hyperion11/Toyota-Prado-OBD1-Computer/source/TOBD1_STM32/atf_temp_sensor_1.png

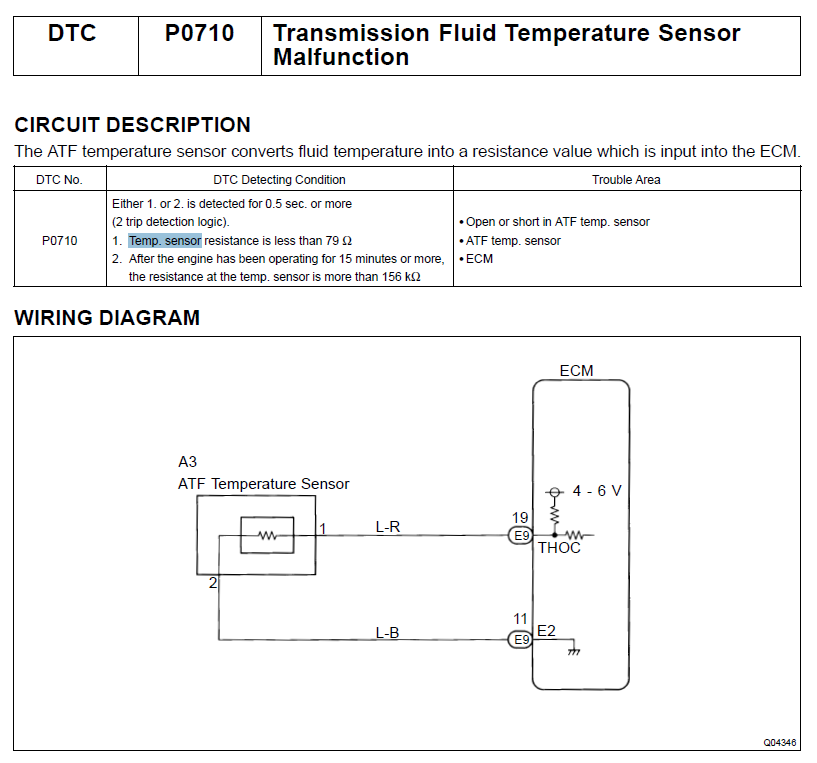
source/TOBD1_STM32/atf_temp_sensor_1.png
