hyperion11/Toyota-Prado-OBD1-Computer/BK Model/крепеж_дисплея_v2.3.STEP

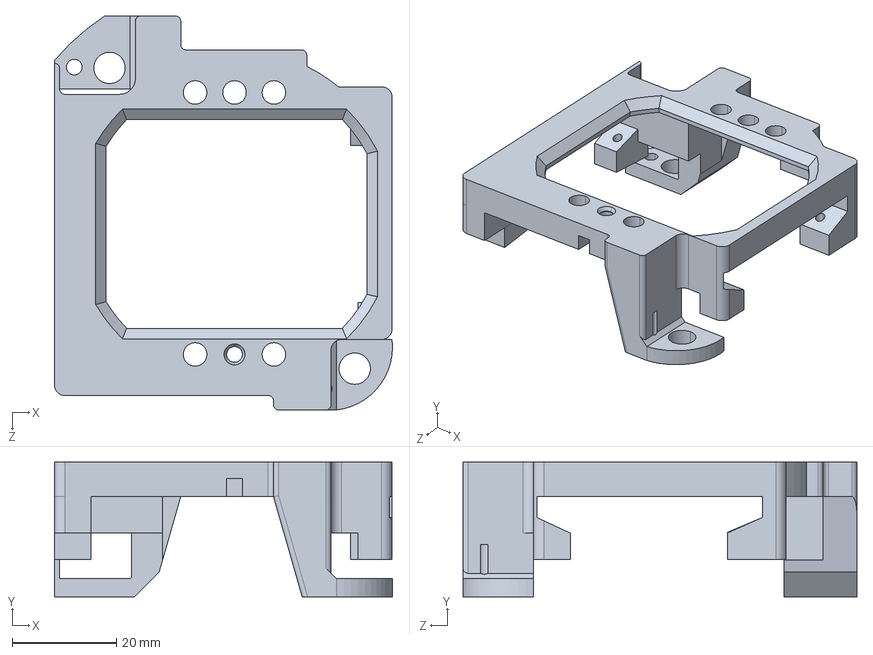
[picture p21: CAD file, 2021-05-25]
BK Model/крепеж_дисплея_v2.3.STEP
64.8 x 25.8 x 75.5 mm
