hyperion11/Toyota-Prado-OBD1-Computer/BK Model/крепеж_дисплея_1_v4.SLDPRT

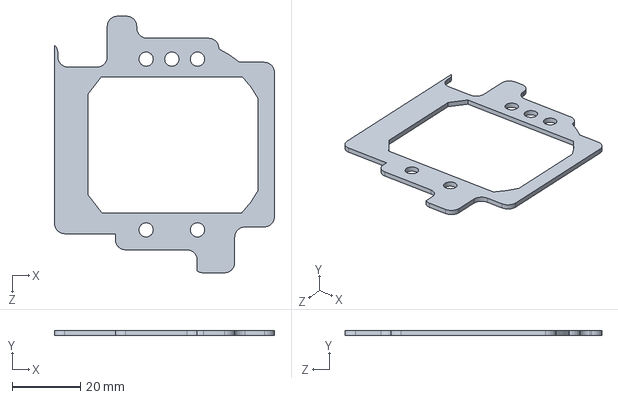
[picture p22: CAD file, 2021-05-25]
BK Model/крепеж_дисплея_1_v4.SLDPRT
64.7 x 1.50 x 75.5 mm
