hyperion11/Toyota-Prado-OBD1-Computer/BK Model/front_shield.SLDPRT

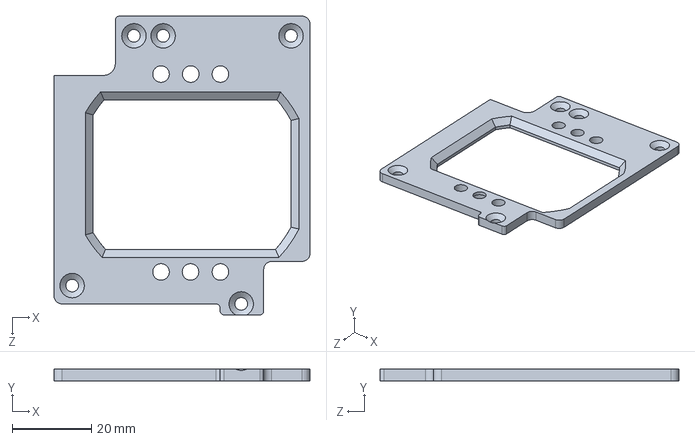
[picture p23: CAD file, 2021-05-25]
BK Model/front_shield.SLDPRT
64.7 x 3.00 x 75.5 mm
