hyperion11/Toyota-Prado-OBD1-Computer/BK Model/pcb_shield.SLDPRT

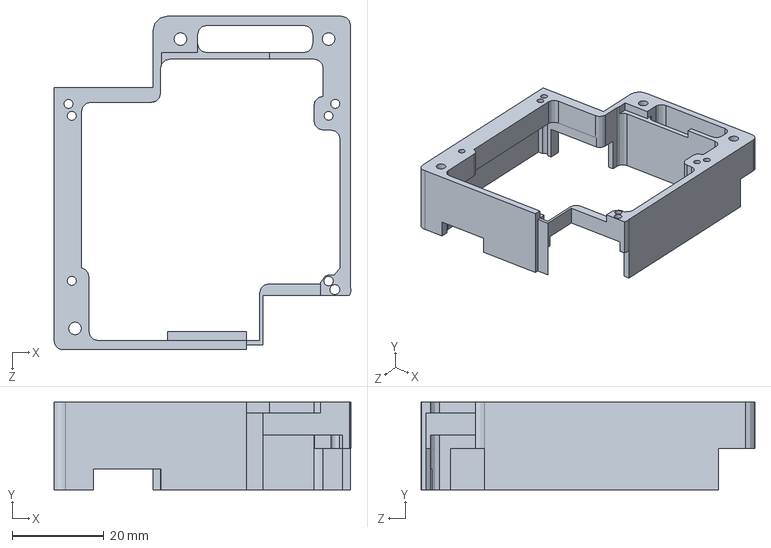
[picture p24: CAD file, 2021-05-25]
BK Model/pcb_shield.SLDPRT
64.8 x 19.1 x 72.8 mm
