hyperion11/Toyota-Prado-OBD1-Computer/source/TOBD1_STM32/src/CPMonoP9pt7b.h

const uint8_t CPMono_v07_Plain9pt7bBitmaps[] PROGMEM = {
  0xFF, 0xFF, 0xCF, 0xDE, 0xF7, 0xB0, 0x36, 0x1B, 0x3F, 0xFF, 0xF3, 0x67,
  0xBF, 0xFE, 0x6C, 0x36, 0x00, 0x0C, 0x3F, 0x9F, 0xF8, 0x3C, 0x06, 0x01,
  0xFC, 0x7F, 0x01, 0x80, 0xF0, 0x6F, 0xF7, 0xF0, 0x60, 0xF0, 0x90, 0x90,
  0x90, 0xF1, 0x07, 0x1C, 0xE0, 0x9E, 0x13, 0x13, 0x13, 0x13, 0x1E, 0x7F,
  0x0F, 0xF3, 0x06, 0x60, 0x0C, 0x18, 0xF7, 0xDE, 0x7E, 0x0C, 0xC1, 0x98,
  0x31, 0xFE, 0x3F, 0x80, 0xFF, 0x7B, 0xF1, 0x8C, 0x63, 0x18, 0xC6, 0x31,
  0x8C, 0x63, 0x0F, 0x78, 0xF7, 0xC6, 0x31, 0x8C, 0x63, 0x18, 0xC6, 0x31,
  0x8C, 0x7F, 0xF0, 0x0C, 0x06, 0x1B, 0x6F, 0xE1, 0xC3, 0xF9, 0xB6, 0x18,
  0x0C, 0x00, 0x18, 0x18, 0x18, 0x18, 0xFF, 0xFF, 0x18, 0x18, 0x18, 0x6C,
  0xE0, 0xFF, 0xF0, 0xF0, 0x06, 0x0C, 0x18, 0x60, 0xC1, 0x86, 0x0C, 0x18,
  0x60, 0xC1, 0x86, 0x0C, 0x18, 0x60, 0x7F, 0x7F, 0xF0, 0x78, 0x3C, 0x1E,
  0x0F, 0x07, 0x83, 0xC1, 0xE0, 0xFF, 0xEF, 0xE0, 0xF8, 0x7C, 0x06, 0x03,
  0x01, 0x80, 0xC0, 0x60, 0x30, 0x18, 0x0C, 0x3F, 0xFF, 0xF0, 0x7F, 0x3F,
  0xEC, 0x19, 0x06, 0x01, 0x80, 0xC0, 0x60, 0x70, 0x38, 0x1C, 0x0F, 0xFF,
  0xFF, 0x7F, 0x7F, 0xF0, 0x60, 0x30, 0x18, 0xFC, 0x7E, 0x03, 0x01, 0xE0,
  0xFF, 0xEF, 0xE0, 0x07, 0x03, 0xC0, 0xF0, 0x6C, 0x33, 0x1C, 0xCE, 0x33,
  0xFF, 0xFF, 0xC0, 0xC0, 0x30, 0x0C, 0xFF, 0xFF, 0xC0, 0xC0, 0xFE, 0xFF,
  0xC3, 0x03, 0x03, 0xC3, 0xFF, 0xFE, 0x7F, 0x3F, 0xF0, 0x78, 0x2C, 0x07,
  0xFB, 0xFF, 0x83, 0xC1, 0xE0, 0xDF, 0xEF, 0xE0, 0xFF, 0xFF, 0xC0, 0x60,
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
  {   395,   8,  12,  11,    2,  -11 },   // 0x46 'F'
  {   407,   9,  12,  11,    1,  -11 },   // 0x47 'G'
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

const GFXfont CPMono_v07_Plain9pt7b PROGMEM = {
  (uint8_t  *)CPMono_v07_Plain9pt7bBitmaps,
  (GFXglyph *)CPMono_v07_Plain9pt7bGlyphs,
  0x20, 0x7E, 25 };

// Approx. 1758 bytes
