hyperion11/Toyota-Prado-OBD1-Computer/source/TOBD1_STM32/src/CPMono_L13pt7b.h

const uint8_t CPMono_v07_Plain13pt7bBitmaps[] PROGMEM = {
  0xFF, 0xFF, 0xFF, 0xFF, 0xFE, 0x3F, 0xE0, 0xCF, 0x9F, 0x3E, 0x7C, 0xE0,
  0x19, 0xC0, 0xCE, 0x06, 0x71, 0xFF, 0xFF, 0xFF, 0x8C, 0x60, 0x63, 0x03,
  0x18, 0xFF, 0xFF, 0xFF, 0xC6, 0x70, 0x33, 0x81, 0x9C, 0x00, 0x06, 0x00,
  0x60, 0x3F, 0xE7, 0xFF, 0xF0, 0xFE, 0x03, 0xE0, 0x0E, 0x00, 0xE0, 0x0F,
  0xFE, 0x7F, 0xF0, 0x07, 0x00, 0x30, 0x03, 0x60, 0x3E, 0x03, 0xF0, 0xF7,
  0xFF, 0x3F, 0xE0, 0x60, 0x06, 0x00, 0x78, 0x1F, 0x82, 0x30, 0x46, 0x08,
  0xC1, 0x18, 0x3F, 0x07, 0xC3, 0x01, 0xE0, 0xF0, 0x70, 0x38, 0x0C, 0x38,
  0x0F, 0xC3, 0x18, 0x63, 0x0C, 0x61, 0x8C, 0x3F, 0x83, 0xE0, 0x7F, 0xE1,
  0xFF, 0xE3, 0xC3, 0xC6, 0x01, 0x8C, 0x00, 0x18, 0x06, 0x38, 0x0C, 0x3E,
  0xFF, 0x7D, 0xFF, 0xC0, 0x63, 0x00, 0xC6, 0x01, 0x8C, 0x03, 0x18, 0x06,
  0x3C, 0x3C, 0x7F, 0xF8, 0x7F, 0xE0, 0xFF, 0xC0, 0x7F, 0xFE, 0x38, 0xE3,
  0x8E, 0x38, 0xE3, 0x8E, 0x38, 0xE3, 0x8E, 0x38, 0xE3, 0x8E, 0x38, 0xE3,
  0xC7, 0xCF, 0xFB, 0xF1, 0xC3, 0x0C, 0x30, 0xC3, 0x0C, 0x30, 0xC3, 0x0C,
  0x30, 0xC3, 0x0C, 0x30, 0xC3, 0x0C, 0xFF, 0xFE, 0x06, 0x00, 0x60, 0x06,
  0x06, 0x67, 0x7E, 0xF1, 0xFC, 0x0F, 0x01, 0xFC, 0x7E, 0xF6, 0x67, 0x06,
  0x00, 0x60, 0x02, 0x00, 0x07, 0x00, 0x70, 0x07, 0x00, 0x70, 0x07, 0x0F,
  0xFF, 0xFF, 0xF0, 0x70, 0x07, 0x00, 0x70, 0x07, 0x00, 0x70, 0x77, 0x73,
  0x36, 0xFF, 0xFF, 0xFF, 0x80, 0x00, 0xC0, 0x70, 0x18, 0x0E, 0x03, 0x80,
  0xC0, 0x70, 0x1C, 0x06, 0x03, 0x80, 0xE0, 0x30, 0x1C, 0x06, 0x01, 0x80,
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
  {   765,  12,  17,  17,    3,  -16 },   // 0x46 'F'
  {   791,  13,  17,  17,    2,  -16 },   // 0x47 'G'
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

const GFXfont CPMono_v07_Plain13pt7b PROGMEM = {
  (uint8_t  *)CPMono_v07_Plain13pt7bBitmaps,
  (GFXglyph *)CPMono_v07_Plain13pt7bGlyphs,
  0x20, 0x7E, 36 };

// Approx. 2808 bytes
