hyperion11/Toyota-Prado-OBD1-Computer/source/TOBD1_STM32/src/DSEG7ModernMini-Bold13pt7b.h

const uint8_t DSEG7ModernMini_Bold13pt7bBitmaps[] PROGMEM = {
  0xFF, 0x06, 0x0C, 0x18, 0x30, 0x60, 0xC1, 0x83, 0x06, 0x0C, 0x18, 0x30,
  0x60, 0xC1, 0xFE, 0xFF, 0x06, 0x0C, 0x18, 0x30, 0x60, 0xC1, 0x83, 0x06,
  0x0C, 0x18, 0x30, 0x60, 0xC1, 0xFE, 0xFF, 0x06, 0x0C, 0x18, 0x30, 0x60,
  0xC1, 0x83, 0x06, 0x0C, 0x18, 0x30, 0x60, 0xC1, 0xFE, 0xFF, 0x06, 0x0C,
  0x18, 0x30, 0x60, 0xC1, 0x83, 0x06, 0x0C, 0x18, 0x30, 0x60, 0xC1, 0xFE,
  0xFF, 0x06, 0x0C, 0x18, 0x30, 0x60, 0xC1, 0x83, 0x06, 0x0C, 0x18, 0x30,
  0x60, 0xC1, 0xFE, 0xFF, 0x06, 0x0C, 0x18, 0x30, 0x60, 0xC1, 0x83, 0x06,
  0x0C, 0x18, 0x30, 0x60, 0xC1, 0xFE, 0xFF, 0x06, 0x0C, 0x18, 0x30, 0x60,
  0xC1, 0x83, 0x06, 0x0C, 0x18, 0x30, 0x60, 0xC1, 0xFE, 0xFF, 0x06, 0x0C,
  0x18, 0x30, 0x60, 0xC1, 0x83, 0x06, 0x0C, 0x18, 0x30, 0x60, 0xC1, 0xFE,
  0xFF, 0x06, 0x0C, 0x18, 0x30, 0x60, 0xC1, 0x83, 0x06, 0x0C, 0x18, 0x30,
  0x60, 0xC1, 0xFE, 0xFF, 0x06, 0x0C, 0x18, 0x30, 0x60, 0xC1, 0x83, 0x06,
  0x0C, 0x18, 0x30, 0x60, 0xC1, 0xFE, 0xFF, 0x06, 0x0C, 0x18, 0x30, 0x60,
  0xC1, 0x83, 0x06, 0x0C, 0x18, 0x30, 0x60, 0xC1, 0xFE, 0x7F, 0xFF, 0xBF,
  0x80, 0x6F, 0x60, 0xFF, 0x06, 0x0C, 0x18, 0x30, 0x60, 0xC1, 0x83, 0x06,
  0x0C, 0x18, 0x30, 0x60, 0xC1, 0xFE, 0x3F, 0xFC, 0x8F, 0xFC, 0xE3, 0xF9,
  0xF0, 0x03, 0xF0, 0x03, 0xF0, 0x07, 0xF0, 0x07, 0xF0, 0x07, 0xF0, 0x07,
  0xF0, 0x07, 0xF0, 0x01, 0xE0, 0x00, 0x60, 0x03, 0x00, 0x07, 0x80, 0x07,
  0xE0, 0x07, 0xF0, 0x07, 0xF0, 0x07, 0xF0, 0x07, 0xE0, 0x07, 0xE0, 0x07,
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
  {   995,  16,  25,  20,    2,  -24 },   // 0x47 'G'
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

const GFXfont DSEG7ModernMini_Bold13pt7b PROGMEM = {
  (uint8_t  *)DSEG7ModernMini_Bold13pt7bBitmaps,
  (GFXglyph *)DSEG7ModernMini_Bold13pt7bGlyphs,
  0x20, 0x7E, 27 };

// Approx. 3722 bytes
