hyperion11/Toyota-Prado-OBD1-Computer/source/TOBD1_STM32/src/CPMono_L6pt7b.h

const uint8_t CPMono_v07_Light6pt7bBitmaps[] PROGMEM = {
  0xFD, 0xB4, 0x53, 0xF5, 0x3F, 0x51, 0x40, 0x23, 0xE8, 0x60, 0xF8, 0x10,
  0x61, 0xF8, 0x80, 0xE2, 0x8A, 0x39, 0x19, 0x89, 0x89, 0x24, 0x60, 0x7C,
  0x84, 0x84, 0x6F, 0x84, 0x84, 0x84, 0x7C, 0xC0, 0x72, 0x49, 0x24, 0x92,
  0x30, 0xE4, 0x92, 0x49, 0x24, 0xF0, 0x22, 0x87, 0x9E, 0xA0, 0x80, 0x20,
  0x82, 0x3F, 0x20, 0x80, 0xE0, 0xF0, 0x80, 0x08, 0x44, 0x23, 0x10, 0x88,
  0x42, 0x00, 0xFA, 0x18, 0x61, 0x86, 0x18, 0x7E, 0x70, 0x41, 0x04, 0x10,
  0x41, 0x3F, 0xFA, 0x10, 0x42, 0x10, 0x84, 0x3F, 0xFA, 0x10, 0x4E, 0x04,
  0x18, 0x7E, 0x0C, 0x0C, 0x14, 0x24, 0x44, 0xFF, 0x04, 0x04, 0xFE, 0x08,
  0x3E, 0x84, 0x18, 0x7E, 0xFA, 0x18, 0x3E, 0x86, 0x18, 0x7E, 0xFC, 0x20,
  0x84, 0x10, 0x82, 0x18, 0xFA, 0x18, 0x7E, 0x86, 0x18, 0x7E, 0xFA, 0x18,
  0x61, 0xFC, 0x18, 0x7E, 0x84, 0x87, 0x09, 0xB0, 0x60, 0x80, 0xF8, 0x3E,
  0xC1, 0x82, 0x6C, 0x00, 0xFA, 0x10, 0x4E, 0x20, 0x80, 0x08, 0xFE, 0x81,
  0xBD, 0xA5, 0xA5, 0xBE, 0x80, 0xFE, 0x18, 0x30, 0xB1, 0x27, 0xE8, 0x70,
  0xE1, 0xFA, 0x18, 0x7E, 0x86, 0x18, 0x7E, 0xFA, 0x18, 0x20, 0x82, 0x08,
  0x7E, 0xFA, 0x18, 0x61, 0x86, 0x18, 0x7E, 0xFE, 0x08, 0x3E, 0x82, 0x08,
  0x3F, 0xFE, 0x08, 0x20, 0xFA, 0x08, 0x20, 0xFA, 0x18, 0x20, 0x9E, 0x18,
  0x7E, 0x86, 0x18, 0x7F, 0x86, 0x18, 0x61, 0xFC, 0x82, 0x08, 0x20, 0x82,
  0x3F, 0xFC, 0x10, 0x41, 0x06, 0x18, 0x7E, 0x8E, 0x69, 0x2C, 0xDA, 0x38,
  0x61, 0x82, 0x08, 0x20, 0x82, 0x08, 0x3F, 0x86, 0x3C, 0xED, 0xA6, 0x18,
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
  {   181,   6,   8,   8,    1,   -7 },   // 0x46 'F'
  {   187,   6,   8,   8,    1,   -7 },   // 0x47 'G'
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

const GFXfont CPMono_v07_Light6pt7b PROGMEM = {
  (uint8_t  *)CPMono_v07_Light6pt7bBitmaps,
  (GFXglyph *)CPMono_v07_Light6pt7bGlyphs,
  0x20, 0x7E, 16 };

// Approx. 1163 bytes
